s3c/pwmix/pictures/IMG_20160907_095537.jpg

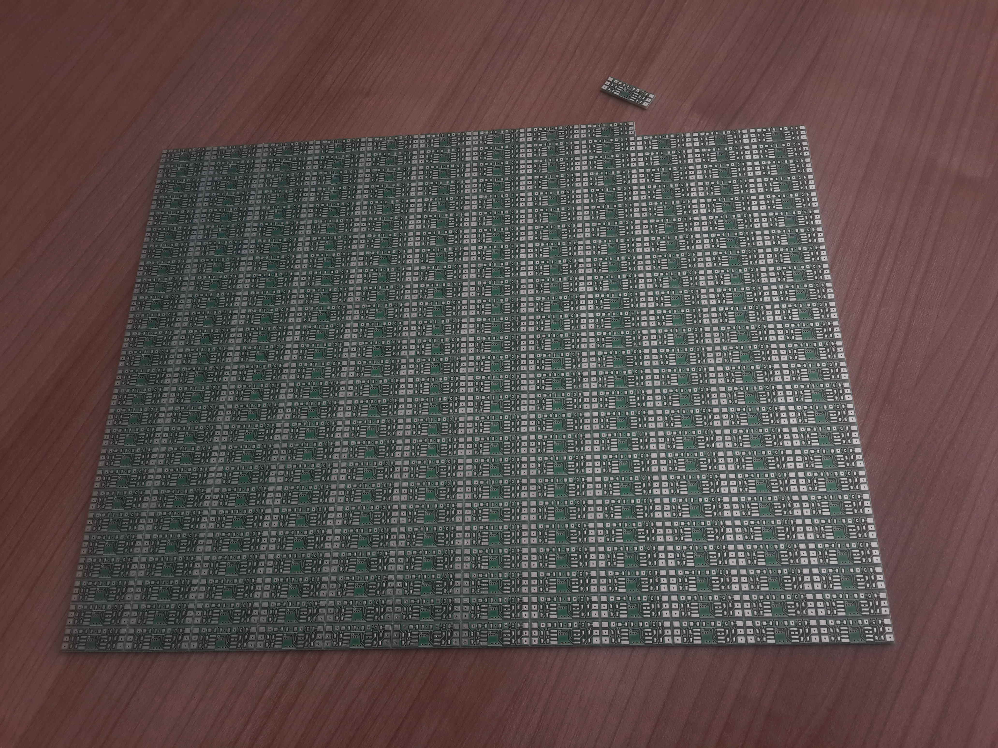
pictures/IMG_20160907_095537.jpg
