s3c/pwmix/pictures/IMG_20160917_153053.jpg

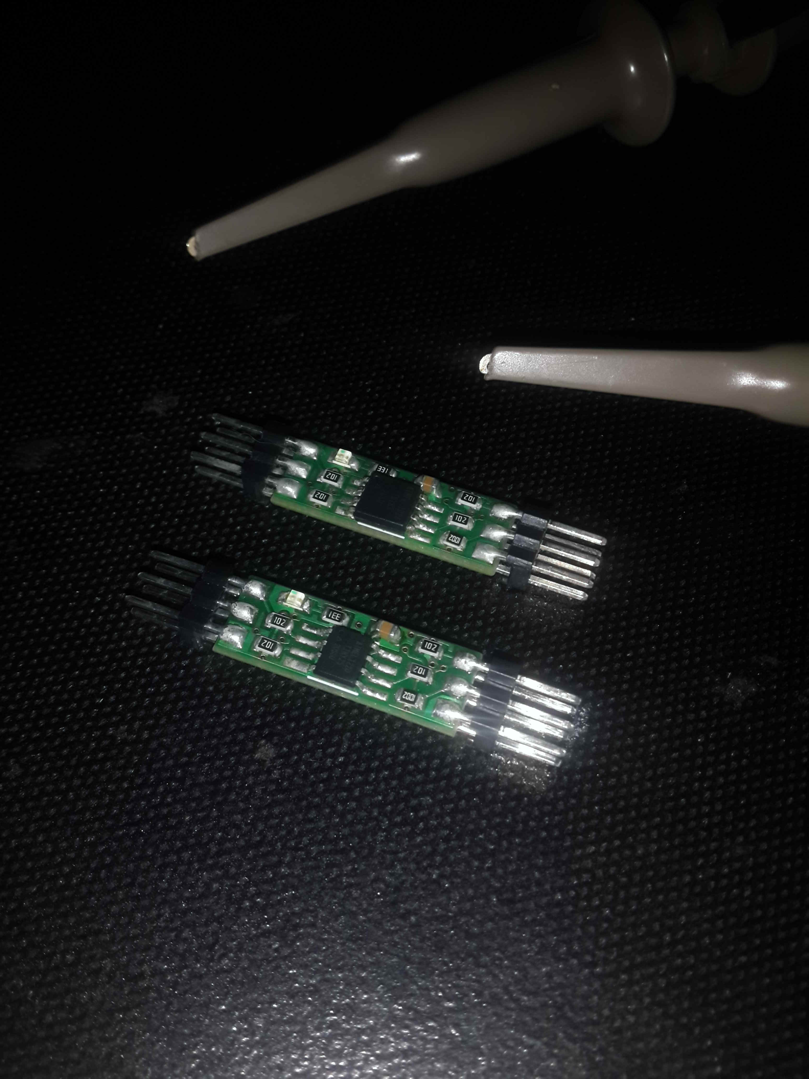
pictures/IMG_20160917_153053.jpg
